adamgreen/BleHidKeyboard/images/20180507-03.jpg

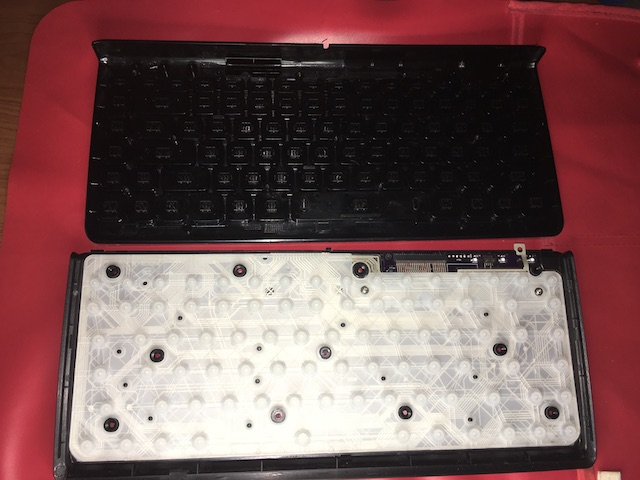
images/20180507-03.jpg
