adamgreen/BleHidKeyboard/firmware/MCP23018.c

/*  Copyright (C) 2017  Adam Green (https://github.com/adamgreen)

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
    This program is distributed in the hope that it will be useful,
    but WITHOUT ANY WARRANTY; without even the implied warranty of
    MERCHANTABILITY or FITNESS FOR A PARTICULAR PURPOSE.  See the
    GNU General Public License for more details.
*/
/* MCP23018 - I2C based 16-Bit I/O Expander with Open-Drain Outputs. */
#include "MCP23018.h"
#include <app_util_platform.h>
#include <nrf_assert.h>
#include <stdlib.h>
#include <string.h>


// MCP23018 Registers when using default BANK (BANK0).
#define MCP23018_IODIRA_REGISTER        0x00
#define MCP23018_IODIRB_REGISTER        0x01
#define MCP23018_IPOLA_REGISTER         0x02
#define MCP23018_IPOLB_REGISTER         0x03
#define MCP23018_GPINTENA_REGISTER      0x04
#define MCP23018_GPINTENB_REGISTER      0x05
#define MCP23018_DEFVALA_REGISTER       0x06
#define MCP23018_DEFVALB_REGISTER       0x07
#define MCP23018_INTCONA_REGISTER       0x08
#define MCP23018_INTCONB_REGISTER       0x09
#define MCP23018_IOCON_REGISTER         0x0A // 0x0B is also valid for this register.
#define MCP23018_GPPUA_REGISTER         0x0C
#define MCP23018_GPPUB_REGISTER         0x0D
#define MCP23018_INTFA_REGISTER         0x0E
#define MCP23018_INTFB_REGISTER         0x0F
#define MCP23018_INTCAPA_REGISTER       0x10
#define MCP23018_INTCAPB_REGISTER       0x11
#define MCP23018_GPIOA_REGISTER         0x12
#define MCP23018_GPIOB_REGISTER         0x13
#define MCP23018_OLATA_REGISTER         0x14
#define MCP23018_OLATB_REGISTER         0x15

// MCP23018_IOCON_REGISTER bits
// Interrupt Clearing Control bit (0: Reading GPIO register clears interrupt. 1: Reading INTCAP clears interrupt.)
#define MCP23018_IOCON_INTCC            (1 << 0)
// Interrupt output Polarity bit (0: Active Low. 1: Active High.)
#define MCP23018_IOCON_INTPOL           (1 << 1)
// Open Drain bit (0: Active driver output. 1: Open-Drain output.)
#define MCP23018_IOCON_ODR              (1 << 2)
// Sequential Operation Mode bit (0: Sequential operation enabled. 1: Sequential operation disabled.)
#define MCP23018_IOCON_SEQOP            (1 << 5)
// Interrupt Mirror bit (0: The INTA/B output pins are not wired together. 
//                       1: The INTA/B output pins are wired OR together.)
#define MCP23018_IOCON_MIRROR           (1 << 6)
// Bank bit (0: The port A and port B registers are sequentially addressed: 1: They aren't sequential.)
#define MCP23018_IOCON_BANK             (1 << 7)


static app_twi_t                     g_twi = APP_TWI_INSTANCE(0);
static const app_twi_transaction_t** g_ppI2cQueue = NULL;
static bool                          g_hasInitCompleted = false;


// Forward Declarations
static void gpioWriteCompletedCallback(ret_code_t result, void* pvContext);
static void gpioReadCompletedCallback(ret_code_t result, void* pvContext);


uint32_t i2cInit(uint32_t sclPin, uint32_t sdaPin, uint8_t transactionQueueSize)
{
    nrf_drv_twi_config_t config =
    {
       .scl                = sclPin,
       .sda                = sdaPin,
       .frequency          = NRF_TWI_FREQ_400K,
       .interrupt_priority = APP_IRQ_PRIORITY_LOW
    };
    uint32_t result;

    if (g_hasInitCompleted)
        return NRF_SUCCESS;

    g_ppI2cQueue = malloc(sizeof(app_twi_transaction_t*) * (transactionQueueSize + 1));
    if (!g_ppI2cQueue)
        return NRF_ERROR_NO_MEM;

    result = app_twi_init(&g_twi, &config, transactionQueueSize, g_ppI2cQueue);
    if (result != NRF_SUCCESS)
    {
        free(g_ppI2cQueue);
        g_ppI2cQueue = NULL;
        return result;
    }
    g_hasInitCompleted = true;

    return NRF_SUCCESS;
}

void i2cUninit(void)
{
    if (g_hasInitCompleted)
    {
        app_twi_uninit(&g_twi);
        free(g_ppI2cQueue);
        g_ppI2cQueue = NULL;
    }
}

uint32_t mcp23018Init(MCP23018* pThis, uint8_t i2cAddress)
{
    ASSERT ( pThis );

    memset(pThis, 0, sizeof(*pThis));
    pThis->i2cAddress = i2cAddress;

    return NRF_SUCCESS;
}

uint32_t mcp23018SetIoConfiguration(MCP23018* pThis,
                                    bool mirrorInterruptOutputs,
                                    bool openDrainInterruptOutputs,
                                    bool interruptActiveHigh,
                                    bool intcapReadClearsInterrupt)
{
    // Default all bits to 0.
    // BANK and SEQOP bits will only be set to 0 because other routines expect them in that state.
    uint8_t configurationValue = 0;

    ASSERT ( pThis );
    
    if (mirrorInterruptOutputs)
        configurationValue |= MCP23018_IOCON_MIRROR;
    if (openDrainInterruptOutputs)
        configurationValue |= MCP23018_IOCON_ODR;
    if (interruptActiveHigh)
        configurationValue |= MCP23018_IOCON_INTPOL;
    if (intcapReadClearsInterrupt)
        configurationValue |= MCP23018_IOCON_INTCC;

    uint8_t setConfiguration[] = { MCP23018_IOCON_REGISTER, configurationValue };
    app_twi_transfer_t transfer[] =
    {
        APP_TWI_WRITE(pThis->i2cAddress, setConfiguration, sizeof(setConfiguration), 0)
    };

    return app_twi_perform(&g_twi, transfer, sizeof(transfer)/sizeof(transfer[0]), NULL);
}

uint32_t mcp23018SetIoDirections(MCP23018* pThis, uint8_t portAInputBits, uint8_t portBInputBits)
{
    ASSERT ( pThis );

    // Uses sequential writes to BANK0 to write both ports at once.
    uint8_t setIoDirection[] = { MCP23018_IODIRA_REGISTER, portAInputBits, portBInputBits };
    app_twi_transfer_t transfer[] =
    {
        APP_TWI_WRITE(pThis->i2cAddress, setIoDirection, sizeof(setIoDirection), 0)
    };

    return app_twi_perform(&g_twi, transfer, sizeof(transfer)/sizeof(transfer[0]), NULL);
}

uint32_t mcp23018SetGpioPullUps(MCP23018* pThis, uint8_t portAPullUpBits, uint8_t portBPullUpBits)
{
    ASSERT ( pThis );

    // Uses sequential writes to BANK0 to write both ports at once.
    uint8_t setPullUps[] = { MCP23018_GPPUA_REGISTER, portAPullUpBits, portBPullUpBits };
    app_twi_transfer_t transfer[] =
    {
        APP_TWI_WRITE(pThis->i2cAddress, setPullUps, sizeof(setPullUps), 0)
    };

    return app_twi_perform(&g_twi, transfer, sizeof(transfer)/sizeof(transfer[0]), NULL);
}

uint32_t mcp23018SetDefaultValues(MCP23018* pThis, uint8_t portADefaultValueBits, uint8_t portBDefaultValueBits)
{
    ASSERT ( pThis );

    // Uses sequential writes to BANK0 to write both ports at once.
    uint8_t setDefaultValues[] = { MCP23018_DEFVALA_REGISTER, portADefaultValueBits, portBDefaultValueBits };
    app_twi_transfer_t transfer[] =
    {
        APP_TWI_WRITE(pThis->i2cAddress, setDefaultValues, sizeof(setDefaultValues), 0)
    };

    return app_twi_perform(&g_twi, transfer, sizeof(transfer)/sizeof(transfer[0]), NULL);
}

uint32_t mcp23018SetInterruptControlValues(MCP23018* pThis,
                                           uint8_t portACompareToDefaultValueBits, 
                                           uint8_t portBCompareToDefaultValueBits)
{
    ASSERT ( pThis );

    // Uses sequential writes to BANK0 to write both ports at once.
    uint8_t setConfigValues[] = 
    { 
        MCP23018_INTCONA_REGISTER,
        portACompareToDefaultValueBits, 
        portBCompareToDefaultValueBits 
    };
    app_twi_transfer_t transfer[] =
    {
        APP_TWI_WRITE(pThis->i2cAddress, setConfigValues, sizeof(setConfigValues), 0)
    };

    return app_twi_perform(&g_twi, transfer, sizeof(transfer)/sizeof(transfer[0]), NULL);
}

uint32_t mcp23018SetGpioInterruptEnables(MCP23018* pThis, 
                                         uint8_t portAInterruptEnableBits, 
                                         uint8_t portBInterruptEnableBits)
{
    ASSERT ( pThis );

    // Uses sequential writes to BANK0 to write both ports at once.
    uint8_t setGpioInterruptEnables[] =
    { 
        MCP23018_GPINTENA_REGISTER,
        portAInterruptEnableBits, 
        portBInterruptEnableBits 
    };
    app_twi_transfer_t transfer[] =
    {
        APP_TWI_WRITE(pThis->i2cAddress, setGpioInterruptEnables, sizeof(setGpioInterruptEnables), 0)
    };

    return app_twi_perform(&g_twi, transfer, sizeof(transfer)/sizeof(transfer[0]), NULL);
}

uint32_t mcp23018AsyncSetGpio(MCP23018* pThis, uint8_t portA, uint8_t portB)
{
    ASSERT ( pThis );

    if (pThis->writeInProgress)
        return NRF_ERROR_BUSY;
        
    // Uses sequential writes to BANK0 to write both ports at once.
    pThis->gpioWrite[0] = MCP23018_GPIOA_REGISTER;
    pThis->gpioWrite[1] = portA;
    pThis->gpioWrite[2] = portB;

    pThis->writeTransfers[0].p_data    = pThis->gpioWrite;
    pThis->writeTransfers[0].length    = sizeof(pThis->gpioWrite);
    pThis->writeTransfers[0].operation = APP_TWI_WRITE_OP(pThis->i2cAddress);
    pThis->writeTransfers[0].flags     = 0;

    pThis->writeTransaction.callback            = gpioWriteCompletedCallback;
    pThis->writeTransaction.p_user_data         = pThis;
    pThis->writeTransaction.p_transfers         = pThis->writeTransfers;
    pThis->writeTransaction.number_of_transfers = 1;

    pThis->writeInProgress = true;
    return app_twi_schedule(&g_twi, &pThis->writeTransaction);
}

static void gpioWriteCompletedCallback(ret_code_t result, void* pvContext)
{
    MCP23018* pThis = (MCP23018*)pvContext;

    ASSERT ( pThis );
    pThis->writeInProgress = false;
}

uint32_t mcp23018AsyncSetOutputAndPullLow(MCP23018* pThis, uint8_t portAMask, uint8_t portBMask)
{
    ASSERT ( pThis );

    if (pThis->writeInProgress)
        return NRF_ERROR_BUSY;

    // The passed in masks have the 0 bit set for which pin should be made an output and then pulled low. All other
    // bits will be 1.
    
    // Uses sequential writes to BANK0 to write both ports at once.
    pThis->setIoDirection[0] = MCP23018_IODIRA_REGISTER;
    pThis->setIoDirection[1] = portAMask;
    pThis->setIoDirection[2] = portBMask;

    pThis->writeTransfers[0].p_data    = pThis->setIoDirection;
    pThis->writeTransfers[0].length    = sizeof(pThis->setIoDirection);
    pThis->writeTransfers[0].operation = APP_TWI_WRITE_OP(pThis->i2cAddress);
    pThis->writeTransfers[0].flags     = 0;

    // Uses sequential writes to BANK0 to write both ports at once.
    pThis->gpioWrite[0] = MCP23018_GPIOA_REGISTER;
    pThis->gpioWrite[1] = portAMask;
    pThis->gpioWrite[2] = portBMask;

    pThis->writeTransfers[1].p_data    = pThis->gpioWrite;
    pThis->writeTransfers[1].length    = sizeof(pThis->gpioWrite);
    pThis->writeTransfers[1].operation = APP_TWI_WRITE_OP(pThis->i2cAddress);
    pThis->writeTransfers[1].flags     = 0;

    pThis->writeTransaction.callback            = gpioWriteCompletedCallback;
    pThis->writeTransaction.p_user_data         = pThis;
    pThis->writeTransaction.p_transfers         = pThis->writeTransfers;
    pThis->writeTransaction.number_of_transfers = 2;

    pThis->writeInProgress = true;
    return app_twi_schedule(&g_twi, &pThis->writeTransaction);
}

uint32_t mcp23018AsyncGetGpio(MCP23018* pThis, uint8_t* pPortA, uint8_t* pPortB)
{
    static const uint8_t gpioRegisterAddress[] = { MCP23018_GPIOA_REGISTER };

    ASSERT ( pThis );

    if (pThis->readInProgress)
        return NRF_ERROR_BUSY;

    // Remember the output buffers so that they can be filled in when the read completes.
    pThis->pPortARead = pPortA;
    pThis->pPortBRead = pPortB;

    // Uses sequential writes to BANK0 to write both ports at once.
    // First transfer is a write with the register address.
    pThis->readTransfers[0].p_data    = (uint8_t*)&gpioRegisterAddress;
    pThis->readTransfers[0].length    = sizeof(gpioRegisterAddress);
    pThis->readTransfers[0].operation = APP_TWI_WRITE_OP(pThis->i2cAddress);
    pThis->readTransfers[0].flags     = APP_TWI_NO_STOP;

    // Second transfer supplies the buffer to read the 2 GPIO ports into.
    pThis->readTransfers[1].p_data    = pThis->gpioRead;
    pThis->readTransfers[1].length    = sizeof(pThis->gpioRead);
    pThis->readTransfers[1].operation = APP_TWI_READ_OP(pThis->i2cAddress);
    pThis->readTransfers[1].flags     = 0;

    pThis->readTransaction.callback            = gpioReadCompletedCallback;
    pThis->readTransaction.p_user_data         = pThis;
    pThis->readTransaction.p_transfers         = pThis->readTransfers;
    pThis->readTransaction.number_of_transfers = sizeof(pThis->readTransfers) / sizeof(pThis->readTransfers[0]);

    pThis->readInProgress = true;
    return app_twi_schedule(&g_twi, &pThis->readTransaction);
}

static void gpioReadCompletedCallback(ret_code_t result, void* pvContext)
{
    MCP23018* pThis = (MCP23018*)pvContext;

    ASSERT ( pThis );

    if (pThis->pPortARead)
        *pThis->pPortARead = pThis->gpioRead[0];
    if (pThis->pPortBRead)
        *pThis->pPortBRead = pThis->gpioRead[1];
    pThis->readInProgress = false;
}

bool mcp23018HasAsyncSetCompleted(MCP23018* pThis)
{
    ASSERT ( pThis );

    return !pThis->writeInProgress;
}

bool mcp23018HasAsyncGetCompleted(MCP23018* pThis)
{
    return !pThis->readInProgress;
}
